FiveTomb/SalmonSpotter/KiCad Project/senior-project.kicad_pcb

## KiCad design resources/KiCad/RFIDwriter/RFIDwriter.kicad_sch

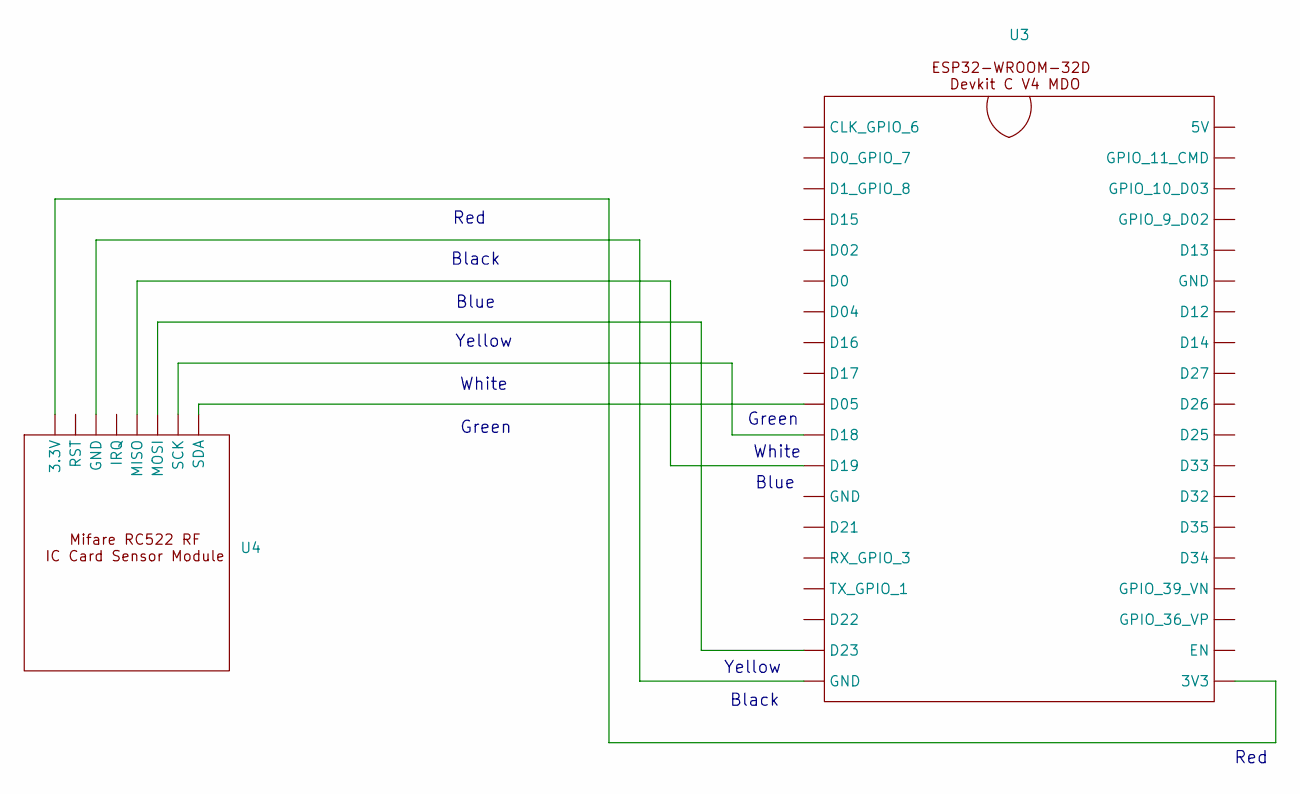
[picture p2: schematic RFIDwriter.kicad_sch]

Parts:
U3, U4: (no value)

Connections:
unnamed: U3., U4.

Notes on the sheet:
Red
Black
Blue
Green
Yellow
White
